AleksandarFilipov/signalbroker-lin-transceiver/doc/Pictures/3d view.PNG

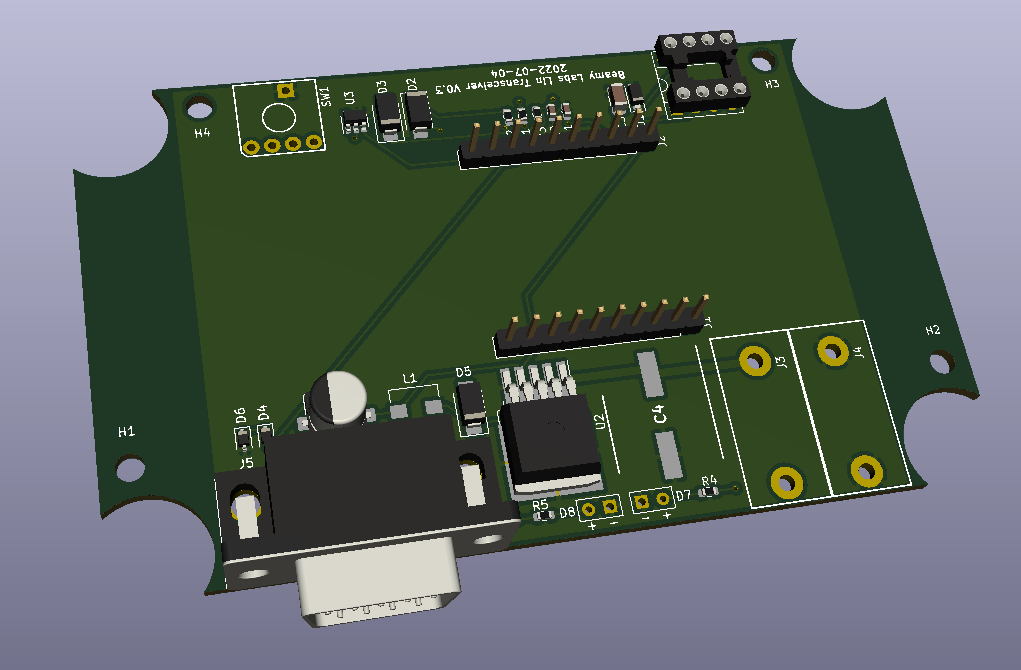
doc/Pictures/3d view.PNG
