AleksandarFilipov/signalbroker-lin-transceiver/doc/Pictures/Both Cards.PNG

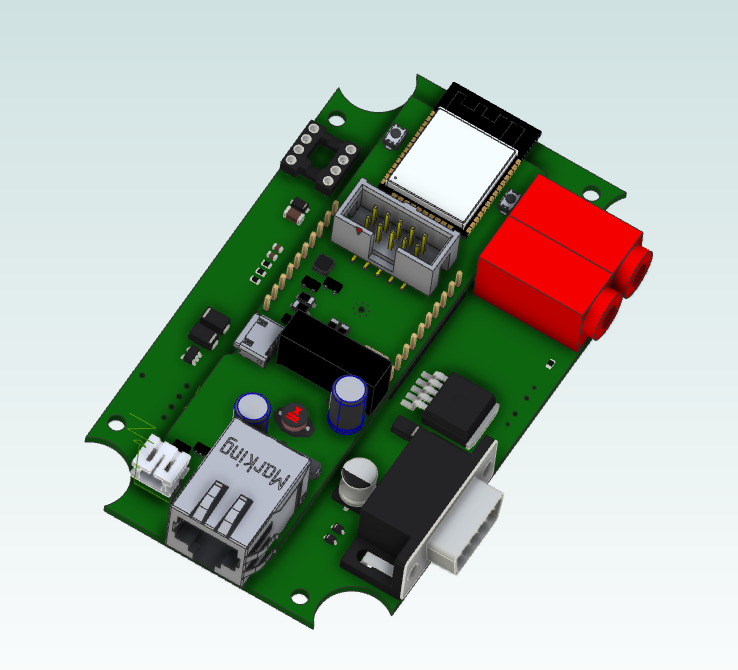
doc/Pictures/Both Cards.PNG
