AleksandarFilipov/signalbroker-lin-transceiver/doc/Pictures/Cards + bottom.PNG

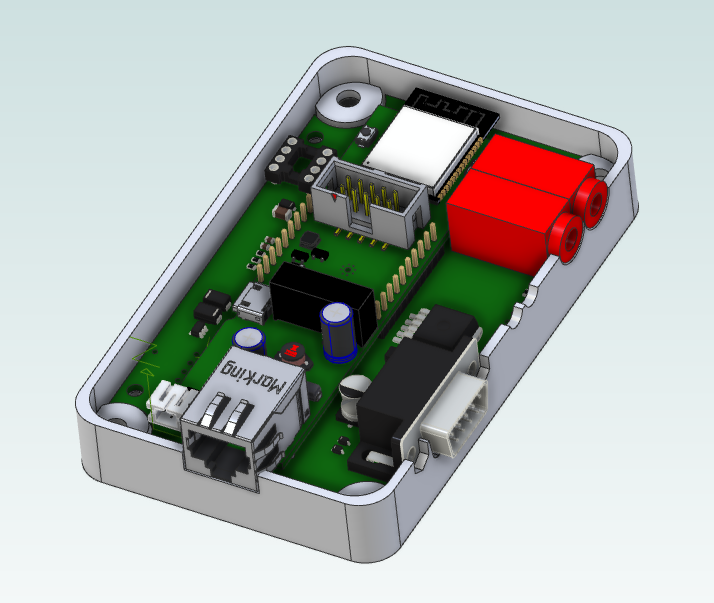
doc/Pictures/Cards + bottom.PNG
