AleksandarFilipov/signalbroker-lin-transceiver/doc/Pictures/PCB.PNG

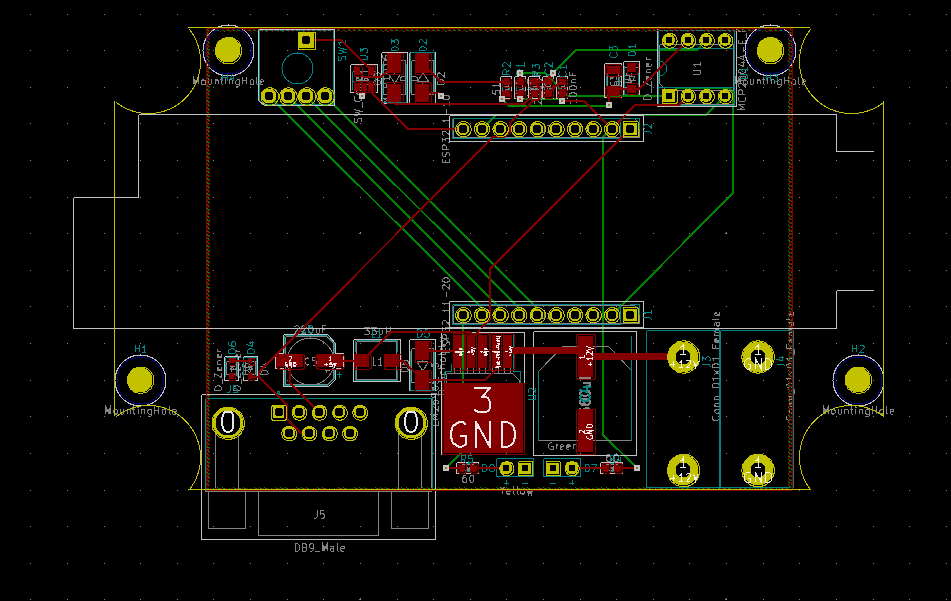
doc/Pictures/PCB.PNG
